posystorage/FLIR-Lepton-PocketThermal/firmware/APP/flir_font_16.c

#include "mcu_font.h"


/*******************************************************************************
 * Tool: MCU_Font V2.0
 * Time: 2026-06-07 22:32:18
 * Bpp: 1
 * LineHeight: 17 px
 * BaseLine: 3
 * 
 * FontCount: 3
 * FontSize_1: 11px  FontFamily_1: Arial  
 * FontSize_2: 12px  FontFamily_2: 宋体  
 * FontSize_3: 12px  FontFamily_3: MS PGothic  
 ******************************************************************************/

#ifndef FLIR_FONT_16
#define FLIR_FONT_16 1
#endif

#if FLIR_FONT_16

/*-----------------
 *    BITMAPS
 *----------------*/

/*Store the image of the glyphs*/
static LV_ATTRIBUTE_LARGE_CONST const uint8_t gylph_bitmap[] = {

    /* U+20 " " */
    0x0, 

    /* U+21 "!" */
    0xff, 0xa0, 

    /* U+23 "#" */
    0x12, 0x12, 0x22, 0xff, 0x24, 0x24, 0x4, 0xff, 
    0x40, 0x48, 0x48, 

    /* U+24 "$" */
    0x0, 0x79, 0x9a, 0x14, 0xe, 0x7, 0x3, 0x2, 
    0x85, 0x9, 0xe0, 0x0, 

    /* U+25 "%" */
    0x60, 0x92, 0x22, 0x40, 0x49, 0x9, 0x0, 0xcb, 
    0x80, 0x48, 0x49, 0x11, 0x22, 0x24, 0x83, 0x0, 

    /* U+26 "&" */
    0x38, 0x22, 0x11, 0xd, 0x83, 0x83, 0x83, 0x25, 
    0x1c, 0x86, 0x63, 0x9e, 0x40, 

    /* U+27 "'" */
    0xf0, 

    /* U+28 "(" */
    0x25, 0x29, 0x24, 0x91, 0x22, 0x40, 

    /* U+29 ")" */
    0x89, 0x12, 0x49, 0x24, 0xa5, 0x0, 

    /* U+2a "*" */
    0x13, 0xcc, 0x74, 0x80, 

    /* U+2b "+" */
    0x10, 0x20, 0x47, 0xf1, 0x2, 0x4, 0x0, 

    /* U+2c "," */
    0x80, 

    /* U+2d "-" */
    0x70, 

    /* U+2e "." */
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
    0x80, 0x43, 0xff, 0x0, 0x0, 0x24, 0x88, 0x89, 
    0x14, 0x24, 0x60, 0x1, 

    /* U+7528 "用" */
    0x3f, 0xf9, 0x8, 0x48, 0x42, 0x42, 0x13, 0xff, 
    0x90, 0x84, 0x84, 0x24, 0x21, 0x3f, 0xf9, 0x8, 
    0x48, 0x42, 0x42, 0x14, 0x10, 0xa0, 0x96, 0x0, 
    0x40, 

    /* U+8bef "误" */
    0x43, 0xf8, 0x44, 0x10, 0x88, 0x20, 0x1f, 0xc0, 
    0x0, 0x1c, 0x0, 0x9, 0xff, 0x10, 0x20, 0x20, 
    0x40, 0x5f, 0xfc, 0x81, 0x1, 0x45, 0x3, 0x11, 
    0x4, 0x41, 0x3, 0x1, 0x80, 

    /* U+8bf7 "请" */
    0x0, 0x40, 0x80, 0x80, 0x9f, 0xf1, 0x2, 0x0, 
    0x3f, 0x80, 0x8, 0x39, 0xff, 0x90, 0x0, 0x23, 
    0xf8, 0x44, 0x10, 0x8f, 0xe1, 0x10, 0x42, 0xbf, 
    0x86, 0x41, 0x8, 0x8a, 0x1, 0x8, 

    /* U+8bfb "读" */
    0x0, 0x20, 0x40, 0x40, 0x47, 0xf0, 0x81, 0x0, 
    0x2, 0x0, 0x7f, 0xfc, 0x0, 0x88, 0x4a, 0x10, 
    0x50, 0x22, 0x20, 0x42, 0x40, 0x9f, 0xf1, 0x42, 
    0x83, 0x8, 0x84, 0x20, 0x81, 0x81, 

    /* U+8d25 "败" */
    0x0, 0x40, 0xf8, 0x81, 0x11, 0x2, 0xa4, 0x5, 
    0x4f, 0xea, 0xa1, 0x15, 0xa2, 0x2a, 0x44, 0x54, 
    0x88, 0xa8, 0xa1, 0x51, 0x40, 0x81, 0x2, 0x85, 
    0x4, 0x91, 0x11, 0x41, 0x41, 0x1, 

    /* U+9519 "错" */
    0x21, 0x10, 0x42, 0x20, 0xe4, 0x41, 0x3f, 0xe4, 
    0x11, 0xf, 0x22, 0x2b, 0xff, 0x90, 0x0, 0xfb, 
    0xf8, 0x44, 0x10, 0x88, 0x21, 0x1f, 0xc2, 0xa0, 
    0x86, 0x41, 0x8, 0xfe, 0x1, 0x4, 

    /* U+9ad8 "高" */
    0x2, 0x0, 0x2, 0x3, 0xff, 0xf8, 0x0, 0x0, 
    0xfe, 0x1, 0x4, 0x2, 0x8, 0x7, 0xf0, 0x0, 
    0x0, 0xff, 0xf9, 0x0, 0x12, 0x7f, 0x24, 0x82, 
    0x49, 0x4, 0x93, 0xf9, 0x20, 0x6, 
};

/*---------------------
 *  GLYPH DESCRIPTION
 *--------------------*/

static const lv_font_fmt_txt_glyph_dsc_t glyph_dsc[] = {
/* id = 0 reserved */  {.bitmap_index = 0, .adv_w = 0, .box_w = 0, .box_h = 0, .ofs_x = 0, .ofs_y = 0},
/* U+20 " " */  {.bitmap_index = 0, .adv_w = 56, .box_w = 1, .box_h = 1, .ofs_x = 0, .ofs_y = -1},
/* U+21 "!" */  {.bitmap_index = 1, .adv_w = 72, .box_w = 1, .box_h = 11, .ofs_x = 2, .ofs_y = 0},
/* U+23 "#" */  {.bitmap_index = 3, .adv_w = 120, .box_w = 8, .box_h = 11, .ofs_x = 0, .ofs_y = 0},
/* U+24 "$" */  {.bitmap_index = 14, .adv_w = 120, .box_w = 7, .box_h = 13, .ofs_x = 0, .ofs_y = -1},
/* U+25 "%" */  {.bitmap_index = 26, .adv_w = 200, .box_w = 11, .box_h = 11, .ofs_x = 1, .ofs_y = 0},
/* U+26 "&" */  {.bitmap_index = 42, .adv_w = 152, .box_w = 9, .box_h = 11, .ofs_x = 1, .ofs_y = 0},
/* U+27 "'" */  {.bitmap_index = 55, .adv_w = 40, .box_w = 1, .box_h = 4, .ofs_x = 1, .ofs_y = 7},
/* U+28 "(" */  {.bitmap_index = 56, .adv_w = 72, .box_w = 3, .box_h = 14, .ofs_x = 1, .ofs_y = -3},
/* U+29 ")" */  {.bitmap_index = 62, .adv_w = 72, .box_w = 3, .box_h = 14, .ofs_x = 1, .ofs_y = -3},
/* U+2a "*" */  {.bitmap_index = 68, .adv_w = 88, .box_w = 5, .box_h = 5, .ofs_x = 0, .ofs_y = 6},
/* U+2b "+" */  {.bitmap_index = 72, .adv_w = 136, .box_w = 7, .box_h = 7, .ofs_x = 1, .ofs_y = 2},
/* U+2c "," */  {.bitmap_index = 79, .adv_w = 56, .box_w = 1, .box_h = 4, .ofs_x = 2, .ofs_y = -3},
/* U+2d "-" */  {.bitmap_index = 80, .adv_w = 72, .box_w = 4, .box_h = 1, .ofs_x = 0, .ofs_y = 3},
/* U+2e "." */  {.bitmap_index = 81, .adv_w = 24, .box_w = 1, .box_h = 1, .ofs_x = 1, .ofs_y = 0},
/* U+2f "/" */  {.bitmap_index = 82, .adv_w = 56, .box_w = 4, .box_h = 11, .ofs_x = 0, .ofs_y = 0},
/* U+30 "0" */  {.bitmap_index = 88, .adv_w = 120, .box_w = 6, .box_h = 11, .ofs_x = 1, .ofs_y = 0},
/* U+31 "1" */  {.bitmap_index = 97, .adv_w = 120, .box_w = 3, .box_h = 11, .ofs_x = 2, .ofs_y = 0},
/* U+32 "2" */  {.bitmap_index = 102, .adv_w = 120, .box_w = 6, .box_h = 11, .ofs_x = 1, .ofs_y = 0},
/* U+33 "3" */  {.bitmap_index = 111, .adv_w = 120, .box_w = 6, .box_h = 11, .ofs_x = 1, .ofs_y = 0},
/* U+34 "4" */  {.bitmap_index = 120, .adv_w = 120, .box_w = 7, .box_h = 11, .ofs_x = 0, .ofs_y = 0},
/* U+35 "5" */  {.bitmap_index = 130, .adv_w = 120, .box_w = 6, .box_h = 11, .ofs_x = 1, .ofs_y = 0},
/* U+36 "6" */  {.bitmap_index = 139, .adv_w = 120, .box_w = 6, .box_h = 11, .ofs_x = 1, .ofs_y = 0},
/* U+37 "7" */  {.bitmap_index = 148, .adv_w = 120, .box_w = 6, .box_h = 11, .ofs_x = 1, .ofs_y = 0},
/* U+38 "8" */  {.bitmap_index = 157, .adv_w = 120, .box_w = 6, .box_h = 11, .ofs_x = 1, .ofs_y = 0},
/* U+39 "9" */  {.bitmap_index = 166, .adv_w = 120, .box_w = 6, .box_h = 11, .ofs_x = 1, .ofs_y = 0},
/* U+3a ":" */  {.bitmap_index = 175, .adv_w = 56, .box_w = 1, .box_h = 8, .ofs_x = 1, .ofs_y = 0},
/* U+3b ";" */  {.bitmap_index = 176, .adv_w = 56, .box_w = 1, .box_h = 11, .ofs_x = 1, .ofs_y = -3},
/* U+3c "<" */  {.bitmap_index = 178, .adv_w = 136, .box_w = 7, .box_h = 7, .ofs_x = 1, .ofs_y = 2},
/* U+3d "=" */  {.bitmap_index = 185, .adv_w = 136, .box_w = 7, .box_h = 5, .ofs_x = 1, .ofs_y = 3},
/* U+3e ">" */  {.bitmap_index = 190, .adv_w = 136, .box_w = 7, .box_h = 7, .ofs_x = 1, .ofs_y = 2},
/* U+3f "?" */  {.bitmap_index = 197, .adv_w = 120, .box_w = 6, .box_h = 11, .ofs_x = 1, .ofs_y = 0},
/* U+40 "@" */  {.bitmap_index = 206, .adv_w = 232, .box_w = 14, .box_h = 14, .ofs_x = 0, .ofs_y = -3},
/* U+41 "A" */  {.bitmap_index = 231, .adv_w = 136, .box_w = 9, .box_h = 11, .ofs_x = 0, .ofs_y = 0},
/* U+42 "B" */  {.bitmap_index = 244, .adv_w = 152, .box_w = 8, .box_h = 11, .ofs_x = 1, .ofs_y = 0},
/* U+43 "C" */  {.bitmap_index = 255, .adv_w = 168, .box_w = 9, .box_h = 11, .ofs_x = 1, .ofs_y = 0},
/* U+44 "D" */  {.bitmap_index = 268, .adv_w = 168, .box_w = 9, .box_h = 11, .ofs_x = 1, .ofs_y = 0},
/* U+45 "E" */  {.bitmap_index = 281, .adv_w = 152, .box_w = 8, .box_h = 11, .ofs_x = 1, .ofs_y = 0},
/* U+46 "F" */  {.bitmap_index = 292, .adv_w = 136, .box_w = 7, .box_h = 11, .ofs_x = 1, .ofs_y = 0},
/* U+47 "G" */  {.bitmap_index = 302, .adv_w = 168, .box_w = 9, .box_h = 11, .ofs_x = 1, .ofs_y = 0},
/* U+48 "H" */  {.bitmap_index = 315, .adv_w = 152, .box_w = 8, .box_h = 11, .ofs_x = 1, .ofs_y = 0},
/* U+49 "I" */  {.bitmap_index = 326, .adv_w = 40, .box_w = 1, .box_h = 11, .ofs_x = 1, .ofs_y = 0},
/* U+4a "J" */  {.bitmap_index = 328, .adv_w = 104, .box_w = 6, .box_h = 11, .ofs_x = 0, .ofs_y = 0},
/* U+4b "K" */  {.bitmap_index = 337, .adv_w = 152, .box_w = 9, .box_h = 11, .ofs_x = 1, .ofs_y = 0},
/* U+4c "L" */  {.bitmap_index = 350, .adv_w = 120, .box_w = 7, .box_h = 11, .ofs_x = 1, .ofs_y = 0},
/* U+4d "M" */  {.bitmap_index = 360, .adv_w = 168, .box_w = 9, .box_h = 11, .ofs_x = 1, .ofs_y = 0},
/* U+4e "N" */  {.bitmap_index = 373, .adv_w = 152, .box_w = 8, .box_h = 11, .ofs_x = 1, .ofs_y = 0},
/* U+4f "O" */  {.bitmap_index = 384, .adv_w = 184, .box_w = 10, .box_h = 11, .ofs_x = 1, .ofs_y = 0},
/* U+50 "P" */  {.bitmap_index = 398, .adv_w = 152, .box_w = 8, .box_h = 11, .ofs_x = 1, .ofs_y = 0},
/* U+51 "Q" */  {.bitmap_index = 409, .adv_w = 184, .box_w = 10, .box_h = 12, .ofs_x = 1, .ofs_y = -1},
/* U+52 "R" */  {.bitmap_index = 424, .adv_w = 168, .box_w = 9, .box_h = 11, .ofs_x = 1, .ofs_y = 0},
/* U+53 "S" */  {.bitmap_index = 437, .adv_w = 152, .box_w = 8, .box_h = 11, .ofs_x = 1, .ofs_y = 0},
/* U+54 "T" */  {.bitmap_index = 448, .adv_w = 136, .box_w = 9, .box_h = 11, .ofs_x = 0, .ofs_y = 0},
/* U+55 "U" */  {.bitmap_index = 461, .adv_w = 152, .box_w = 8, .box_h = 11, .ofs_x = 1, .ofs_y = 0},
/* U+56 "V" */  {.bitmap_index = 472, .adv_w = 136, .box_w = 9, .box_h = 11, .ofs_x = 0, .ofs_y = 0},
/* U+57 "W" */  {.bitmap_index = 485, .adv_w = 232, .box_w = 15, .box_h = 11, .ofs_x = 0, .ofs_y = 0},
/* U+58 "X" */  {.bitmap_index = 506, .adv_w = 136, .box_w = 9, .box_h = 11, .ofs_x = 0, .ofs_y = 0},
/* U+59 "Y" */  {.bitmap_index = 519, .adv_w = 136, .box_w = 9, .box_h = 11, .ofs_x = 0, .ofs_y = 0},
/* U+5a "Z" */  {.bitmap_index = 532, .adv_w = 120, .box_w = 8, .box_h = 11, .ofs_x = 0, .ofs_y = 0},
/* U+5b "[" */  {.bitmap_index = 543, .adv_w = 56, .box_w = 3, .box_h = 14, .ofs_x = 1, .ofs_y = -3},
/* U+5d "]" */  {.bitmap_index = 549, .adv_w = 56, .box_w = 3, .box_h = 14, .ofs_x = 0, .ofs_y = -3},
/* U+5e "^" */  {.bitmap_index = 555, .adv_w = 72, .box_w = 5, .box_h = 6, .ofs_x = 0, .ofs_y = 5},
/* U+5f "_" */  {.bitmap_index = 559, .adv_w = 120, .box_w = 8, .box_h = 1, .ofs_x = 0, .ofs_y = -3},
/* U+60 "`" */  {.bitmap_index = 560, .adv_w = 72, .box_w = 2, .box_h = 2, .ofs_x = 1, .ofs_y = 9},
/* U+61 "a" */  {.bitmap_index = 561, .adv_w = 120, .box_w = 6, .box_h = 8, .ofs_x = 1, .ofs_y = 0},
/* U+62 "b" */  {.bitmap_index = 567, .adv_w = 120, .box_w = 6, .box_h = 11, .ofs_x = 1, .ofs_y = 0},
/* U+63 "c" */  {.bitmap_index = 576, .adv_w = 120, .box_w = 6, .box_h = 8, .ofs_x = 1, .ofs_y = 0},
/* U+64 "d" */  {.bitmap_index = 582, .adv_w = 120, .box_w = 6, .box_h = 11, .ofs_x = 1, .ofs_y = 0},
/* U+65 "e" */  {.bitmap_index = 591, .adv_w = 120, .box_w = 6, .box_h = 8, .ofs_x = 1, .ofs_y = 0},
/* U+66 "f" */  {.bitmap_index = 597, .adv_w = 56, .box_w = 4, .box_h = 11, .ofs_x = 0, .ofs_y = 0},
/* U+67 "g" */  {.bitmap_index = 603, .adv_w = 120, .box_w = 6, .box_h = 11, .ofs_x = 1, .ofs_y = -3},
/* U+68 "h" */  {.bitmap_index = 612, .adv_w = 120, .box_w = 6, .box_h = 11, .ofs_x = 1, .ofs_y = 0},
/* U+69 "i" */  {.bitmap_index = 621, .adv_w = 40, .box_w = 1, .box_h = 11, .ofs_x = 1, .ofs_y = 0},
/* U+6a "j" */  {.bitmap_index = 623, .adv_w = 40, .box_w = 3, .box_h = 14, .ofs_x = -1, .ofs_y = -3},
/* U+6b "k" */  {.bitmap_index = 629, .adv_w = 104, .box_w = 6, .box_h = 11, .ofs_x = 1, .ofs_y = 0},
/* U+6c "l" */  {.bitmap_index = 638, .adv_w = 40, .box_w = 1, .box_h = 11, .ofs_x = 1, .ofs_y = 0},
/* U+6d "m" */  {.bitmap_index = 640, .adv_w = 200, .box_w = 11, .box_h = 8, .ofs_x = 1, .ofs_y = 0},
/* U+6e "n" */  {.bitmap_index = 651, .adv_w = 120, .box_w = 6, .box_h = 8, .ofs_x = 1, .ofs_y = 0},
/* U+6f "o" */  {.bitmap_index = 657, .adv_w = 120, .box_w = 6, .box_h = 8, .ofs_x = 1, .ofs_y = 0},
/* U+70 "p" */  {.bitmap_index = 663, .adv_w = 120, .box_w = 6, .box_h = 11, .ofs_x = 1, .ofs_y = -3},
/* U+71 "q" */  {.bitmap_index = 672, .adv_w = 120, .box_w = 6, .box_h = 11, .ofs_x = 1, .ofs_y = -3},
/* U+72 "r" */  {.bitmap_index = 681, .adv_w = 72, .box_w = 4, .box_h = 8, .ofs_x = 1, .ofs_y = 0},
/* U+73 "s" */  {.bitmap_index = 685, .adv_w = 120, .box_w = 6, .box_h = 8, .ofs_x = 1, .ofs_y = 0},
/* U+74 "t" */  {.bitmap_index = 691, .adv_w = 56, .box_w = 4, .box_h = 11, .ofs_x = 0, .ofs_y = 0},
/* U+75 "u" */  {.bitmap_index = 697, .adv_w = 120, .box_w = 6, .box_h = 8, .ofs_x = 1, .ofs_y = 0},
/* U+76 "v" */  {.bitmap_index = 703, .adv_w = 104, .box_w = 7, .box_h = 8, .ofs_x = 0, .ofs_y = 0},
/* U+77 "w" */  {.bitmap_index = 710, .adv_w = 168, .box_w = 11, .box_h = 8, .ofs_x = 0, .ofs_y = 0},
/* U+78 "x" */  {.bitmap_index = 721, .adv_w = 104, .box_w = 7, .box_h = 8, .ofs_x = 0, .ofs_y = 0},
/* U+79 "y" */  {.bitmap_index = 728, .adv_w = 104, .box_w = 7, .box_h = 11, .ofs_x = 0, .ofs_y = -3},
/* U+7a "z" */  {.bitmap_index = 738, .adv_w = 120, .box_w = 6, .box_h = 8, .ofs_x = 1, .ofs_y = 0},
/* U+7b "{" */  {.bitmap_index = 744, .adv_w = 72, .box_w = 5, .box_h = 14, .ofs_x = 0, .ofs_y = -3},
/* U+7c "|" */  {.bitmap_index = 753, .adv_w = 40, .box_w = 1, .box_h = 14, .ofs_x = 1, .ofs_y = -3},
/* U+7d "}" */  {.bitmap_index = 755, .adv_w = 72, .box_w = 5, .box_h = 14, .ofs_x = 0, .ofs_y = -3},
/* U+7e "~" */  {.bitmap_index = 764, .adv_w = 136, .box_w = 8, .box_h = 2, .ofs_x = 0, .ofs_y = 4},
/* U+2103 "℃" */  {.bitmap_index = 766, .adv_w = 248, .box_w = 14, .box_h = 15, .ofs_x = 0, .ofs_y = -1},
/* U+4e2d "中" */  {.bitmap_index = 793, .adv_w = 248, .box_w = 11, .box_h = 16, .ofs_x = 2, .ofs_y = -2},
/* U+4f4e "低" */  {.bitmap_index = 815, .adv_w = 248, .box_w = 15, .box_h = 16, .ofs_x = 0, .ofs_y = -2},
/* U+4fdd "保" */  {.bitmap_index = 845, .adv_w = 248, .box_w = 15, .box_h = 16, .ofs_x = 0, .ofs_y = -2},
/* U+5165 "入" */  {.bitmap_index = 875, .adv_w = 248, .box_w = 15, .box_h = 16, .ofs_x = 0, .ofs_y = -2},
/* U+5199 "写" */  {.bitmap_index = 905, .adv_w = 248, .box_w = 15, .box_h = 15, .ofs_x = 0, .ofs_y = -2},
/* U+529f "功" */  {.bitmap_index = 934, .adv_w = 248, .box_w = 14, .box_h = 16, .ofs_x = 0, .ofs_y = -2},
/* U+5361 "卡" */  {.bitmap_index = 962, .adv_w = 248, .box_w = 15, .box_h = 16, .ofs_x = 0, .ofs_y = -2},
/* U+53d6 "取" */  {.bitmap_index = 992, .adv_w = 248, .box_w = 15, .box_h = 15, .ofs_x = 0, .ofs_y = -2},
/* U+5931 "失" */  {.bitmap_index = 1021, .adv_w = 248, .box_w = 15, .box_h = 16, .ofs_x = 0, .ofs_y = -2},
/* U+5b58 "存" */  {.bitmap_index = 1051, .adv_w = 248, .box_w = 15, .box_h = 16, .ofs_x = 0, .ofs_y = -2},
/* U+5fc3 "心" */  {.bitmap_index = 1081, .adv_w = 248, .box_w = 15, .box_h = 14, .ofs_x = 0, .ofs_y = -1},
/* U+6210 "成" */  {.bitmap_index = 1108, .adv_w = 248, .box_w = 15, .box_h = 16, .ofs_x = 0, .ofs_y = -2},
/* U+6237 "户" */  {.bitmap_index = 1138, .adv_w = 248, .box_w = 12, .box_h = 16, .ofs_x = 1, .ofs_y = -2},
/* U+63d2 "插" */  {.bitmap_index = 1162, .adv_w = 248, .box_w = 15, .box_h = 16, .ofs_x = 0, .ofs_y = -2},
/* U+6700 "最" */  {.bitmap_index = 1192, .adv_w = 248, .box_w = 15, .box_h = 16, .ofs_x = 0, .ofs_y = -2},
/* U+6d88 "消" */  {.bitmap_index = 1222, .adv_w = 248, .box_w = 13, .box_h = 16, .ofs_x = 0, .ofs_y = -2},
/* U+6e29 "温" */  {.bitmap_index = 1248, .adv_w = 248, .box_w = 15, .box_h = 14, .ofs_x = 0, .ofs_y = -1},
/* U+70b9 "点" */  {.bitmap_index = 1275, .adv_w = 248, .box_w = 14, .box_h = 16, .ofs_x = 0, .ofs_y = -2},
/* U+7528 "用" */  {.bitmap_index = 1303, .adv_w = 248, .box_w = 13, .box_h = 15, .ofs_x = 0, .ofs_y = -2},
/* U+8bef "误" */  {.bitmap_index = 1328, .adv_w = 248, .box_w = 15, .box_h = 15, .ofs_x = 0, .ofs_y = -2},
/* U+8bf7 "请" */  {.bitmap_index = 1357, .adv_w = 248, .box_w = 15, .box_h = 16, .ofs_x = 0, .ofs_y = -2},
/* U+8bfb "读" */  {.bitmap_index = 1387, .adv_w = 248, .box_w = 15, .box_h = 16, .ofs_x = 0, .ofs_y = -2},
/* U+8d25 "败" */  {.bitmap_index = 1417, .adv_w = 248, .box_w = 15, .box_h = 16, .ofs_x = 0, .ofs_y = -2},
/* U+9519 "错" */  {.bitmap_index = 1447, .adv_w = 248, .box_w = 15, .box_h = 16, .ofs_x = 0, .ofs_y = -2},
/* U+9ad8 "高" */  {.bitmap_index = 1477, .adv_w = 248, .box_w = 15, .box_h = 16, .ofs_x = 0, .ofs_y = -2},
};

/*---------------------
 *  CHARACTER MAPPING
 *--------------------*/

static const uint16_t unicode_list_1[] = {

    0x20, 0x21, 0x23, 0x24, 0x25, 0x26, 0x27, 0x28, 
    0x29, 0x2a, 0x2b, 0x2c, 0x2d, 0x2e, 0x2f, 0x30, 
    0x31, 0x32, 0x33, 0x34, 0x35, 0x36, 0x37, 0x38, 
    0x39, 0x3a, 0x3b, 0x3c, 0x3d, 0x3e, 0x3f, 0x40, 
    0x41, 0x42, 0x43, 0x44, 0x45, 0x46, 0x47, 0x48, 
    0x49, 0x4a, 0x4b, 0x4c, 0x4d, 0x4e, 0x4f, 0x50, 
    0x51, 0x52, 0x53, 0x54, 0x55, 0x56, 0x57, 0x58, 
    0x59, 0x5a, 0x5b, 0x5d, 0x5e, 0x5f, 0x60, 0x61, 
    0x62, 0x63, 0x64, 0x65, 0x66, 0x67, 0x68, 0x69, 
    0x6a, 0x6b, 0x6c, 0x6d, 0x6e, 0x6f, 0x70, 0x71, 
    0x72, 0x73, 0x74, 0x75, 0x76, 0x77, 0x78, 0x79, 
    0x7a, 0x7b, 0x7c, 0x7d, 0x7e, 0x2103, 0x4e2d, 0x4f4e, 
    0x4fdd, 0x5165, 0x5199, 0x529f, 0x5361, 0x53d6, 0x5931, 0x5b58, 
    0x5fc3, 0x6210, 0x6237, 0x63d2, 0x6700, 0x6d88, 0x6e29, 0x70b9, 
    0x7528, 0x8bef, 0x8bf7, 0x8bfb, 0x8d25, 0x9519, 0x9ad8, 
};

/*Collect the unicode lists and glyph_id offsets*/
static const lv_font_fmt_txt_cmap_t cmaps[] =
{
    {
        .range_start = 0, .range_length = 39640, .glyph_id_start = 1,
        .unicode_list = unicode_list_1, .glyph_id_ofs_list = NULL, .list_length = 119, .type = LV_FONT_FMT_TXT_CMAP_SPARSE_TINY
    }
};

/*--------------------
 *  ALL CUSTOM DATA
 *--------------------*/
/*Store all the custom data of the font*/
static lv_font_fmt_txt_dsc_t font_dsc = {
    .glyph_bitmap = gylph_bitmap,
    .glyph_dsc = glyph_dsc,
    .cmaps = cmaps,
    .kern_dsc = NULL,
    .kern_scale = 0,
    .cmap_num = 1,
    .bpp = 1,
    .kern_classes = 0,
    .bitmap_format = 0
};

/*-----------------
 *  PUBLIC FONT
 *----------------*/

/*Initialize a public general font descriptor*/
lv_font_t flir_font_16 = {
    .get_glyph_dsc = lv_font_get_glyph_dsc_fmt_txt,    /*Function pointer to get glyph's data*/
    .get_glyph_bitmap = lv_font_get_bitmap_fmt_txt,    /*Function pointer to get glyph's bitmap*/
    .line_height = 16,          /*The maximum line height required by the font*/
    .base_line = 2,             /*Baseline measured from the bottom of the line*/
#if !(LVGL_VERSION_MAJOR == 6 && LVGL_VERSION_MINOR == 0)
    .subpx = LV_FONT_SUBPX_NONE,
#endif
    .dsc = &font_dsc           /*The custom font data. Will be accessed by `get_glyph_bitmap/dsc` */
};
#endif /*#if FLIR_FONT_16*/
